thanh-duyen/TXRX-2.4GHz/RX_V2_Image_1.JPG

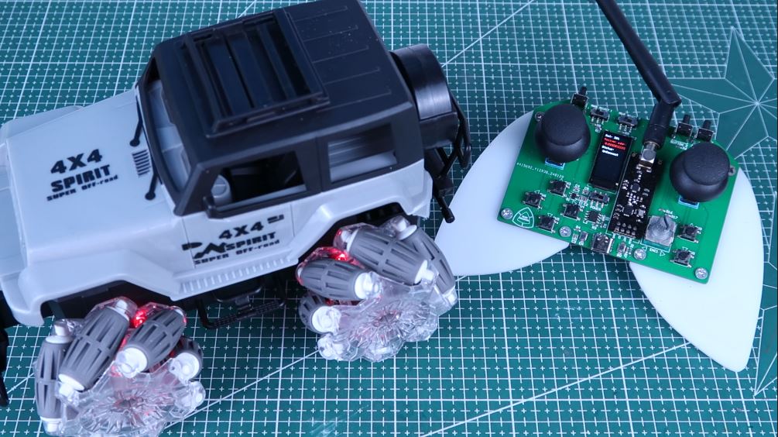
RX_V2_Image_1.JPG
