thanh-duyen/TXRX-2.4GHz/RX_V3_Image_3.JPG

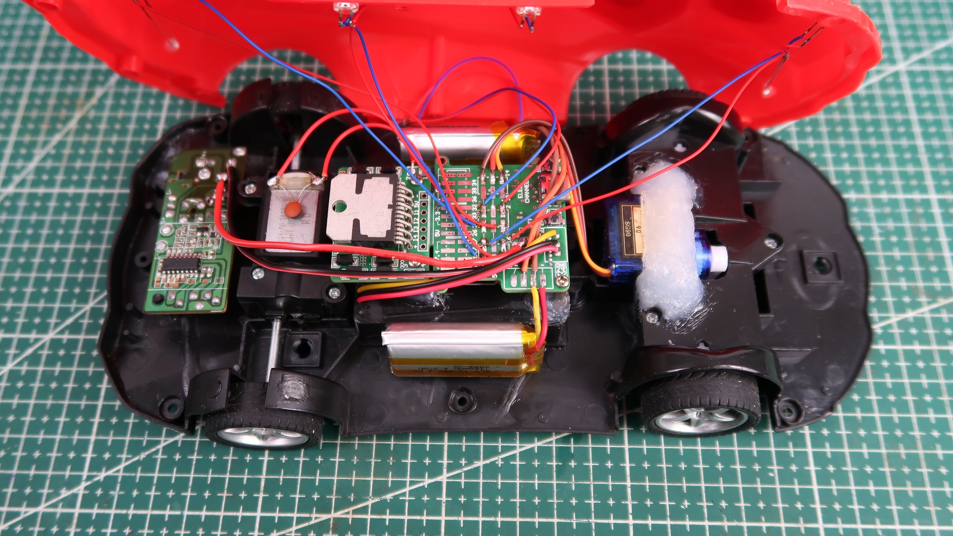
RX_V3_Image_3.JPG
